go4retro/CC40_RAMCart/ref/6eed481904e7582e31d61870e053c0e3.jpg

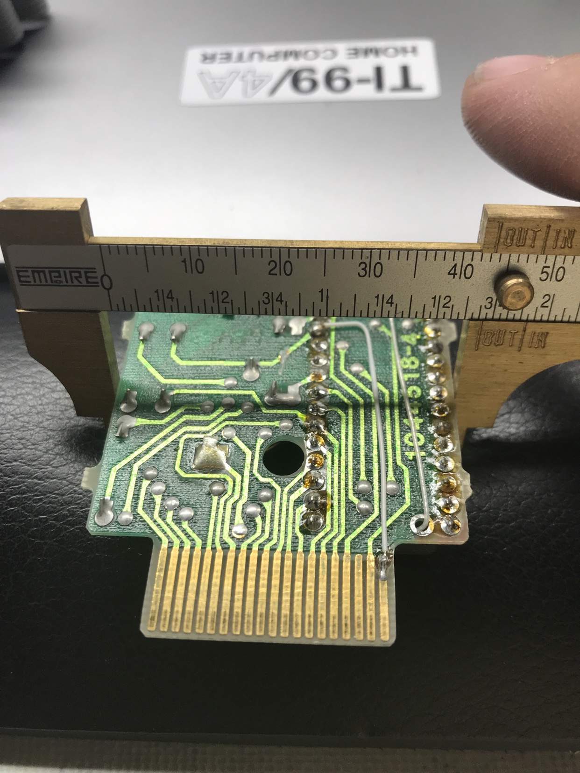
ref/6eed481904e7582e31d61870e053c0e3.jpg
