go4retro/CC40_RAMCart/ref/b44817357aadde21cb518a3dff264925.jpg

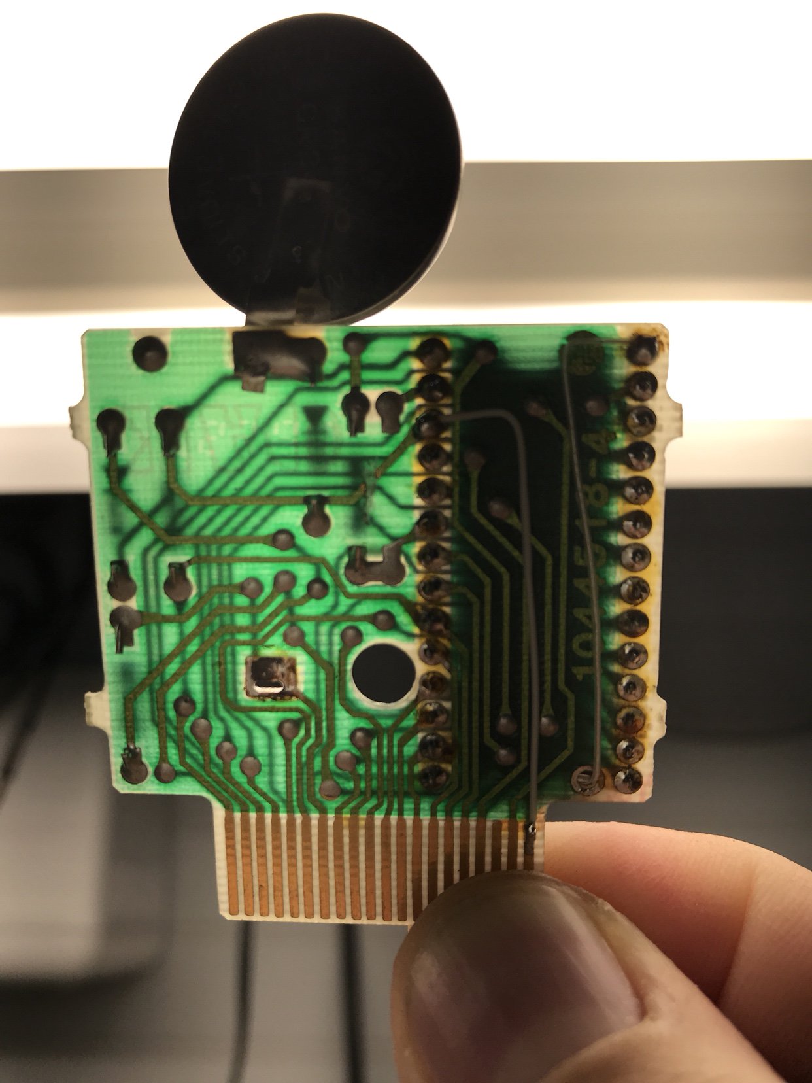
ref/b44817357aadde21cb518a3dff264925.jpg
