go4retro/CC40_RAMCart/ref/baff6df9dfcb7e940d2d8c7732399056.jpg

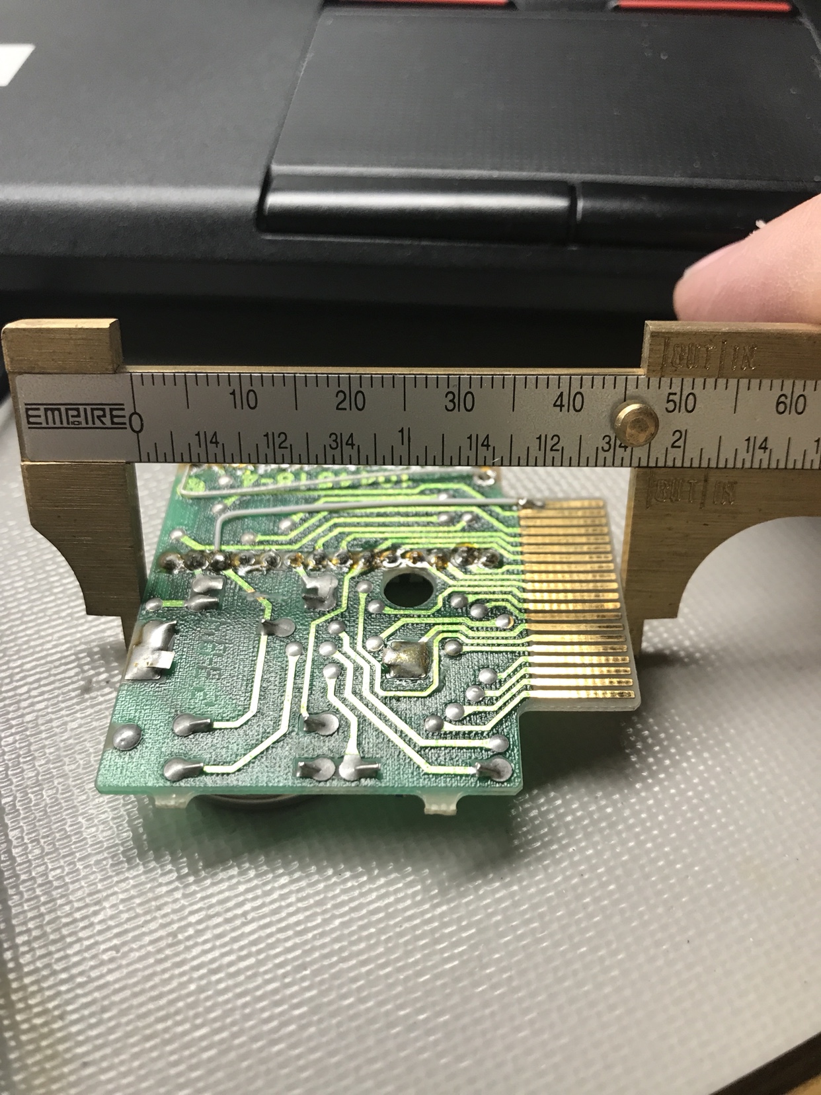
ref/baff6df9dfcb7e940d2d8c7732399056.jpg
