go4retro/CC40_RAMCart/ref/bottom.jpg

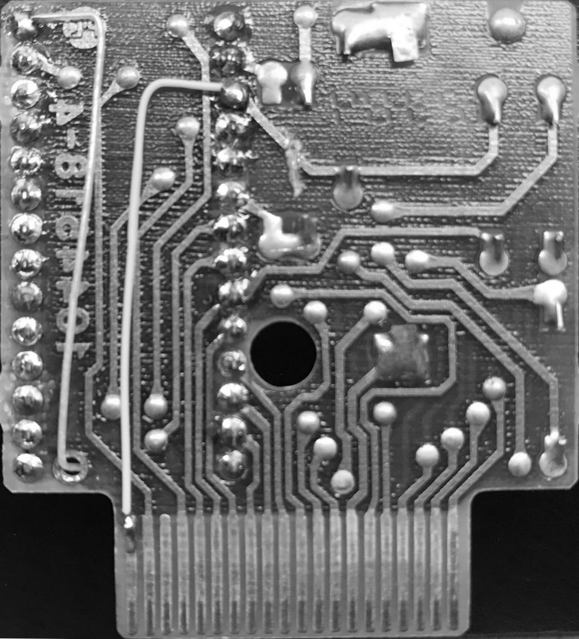
ref/bottom.jpg
