go4retro/CC40_RAMCart/ref/c72c63cf6bb13a48751068caec0abe6d.jpg

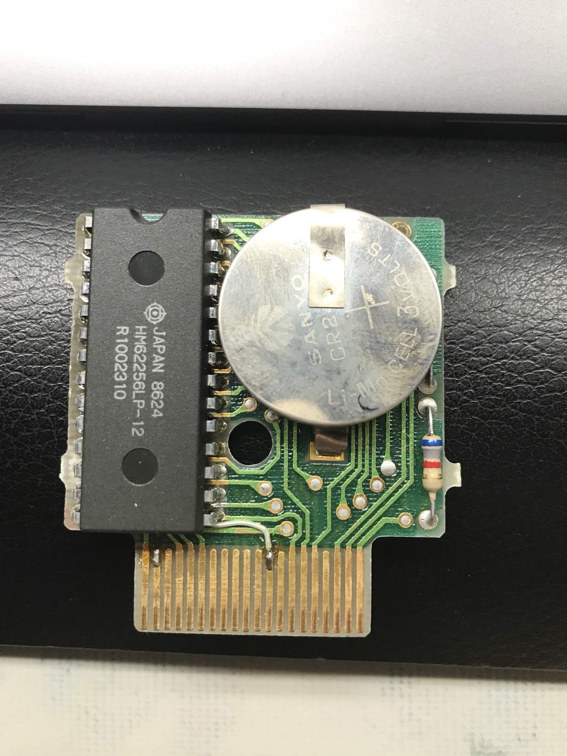
ref/c72c63cf6bb13a48751068caec0abe6d.jpg
