go4retro/CC40_RAMCart/ref/top2.jpg

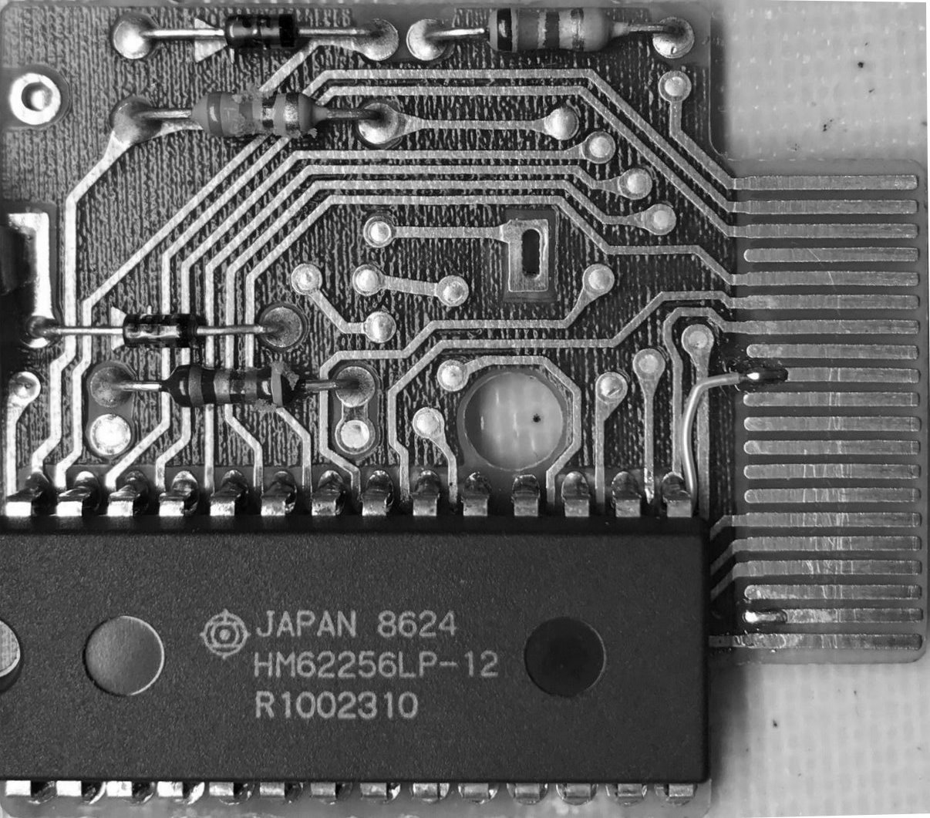
ref/top2.jpg
