go4retro/CC40_RAMCart/ref/top.jpg

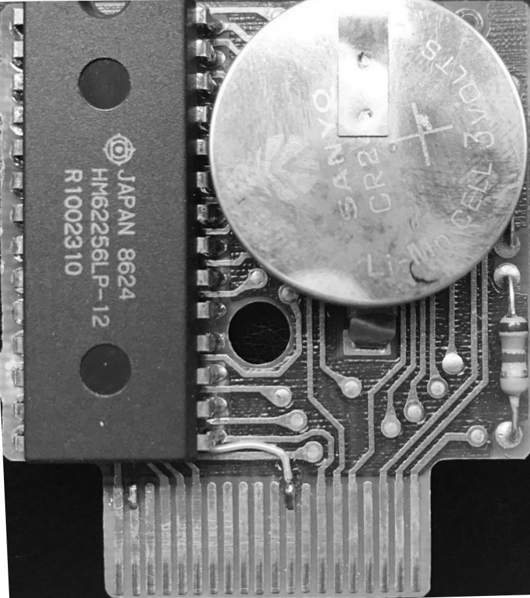
ref/top.jpg
